VEinteligente/asymentric-lock-box/Asymmetric Lock Box/STEP Files/AcrilicoTapa.STEP

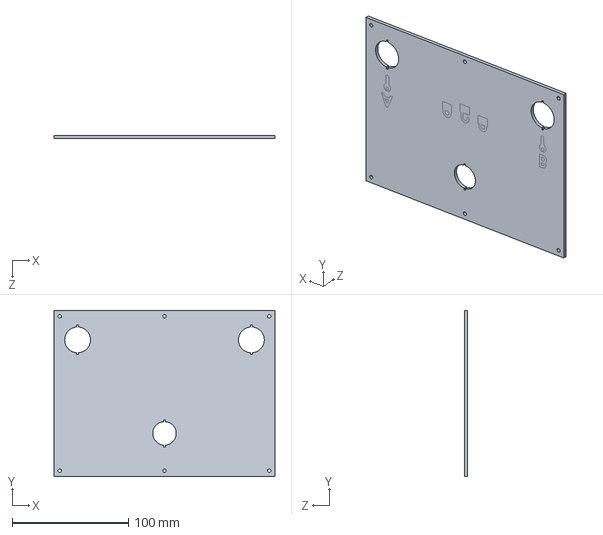
[picture p16: CAD file, 2022-03-03]
Asymmetric Lock Box/STEP Files/AcrilicoTapa.STEP
190.2 x 142.9 x 2.70 mm
