VEinteligente/asymentric-lock-box/Asymmetric Lock Box/STEP Files/BaseCerradura.STEP

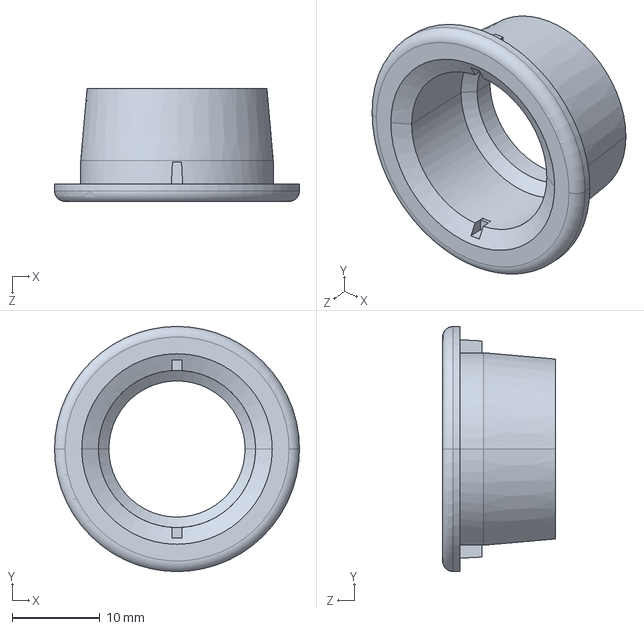
[picture p17: CAD file, 2022-03-03]
Asymmetric Lock Box/STEP Files/BaseCerradura.STEP
28.0 x 28.0 x 12.9 mm
