VEinteligente/asymentric-lock-box/Asymmetric Lock Box/STEP Files/Leva.STEP

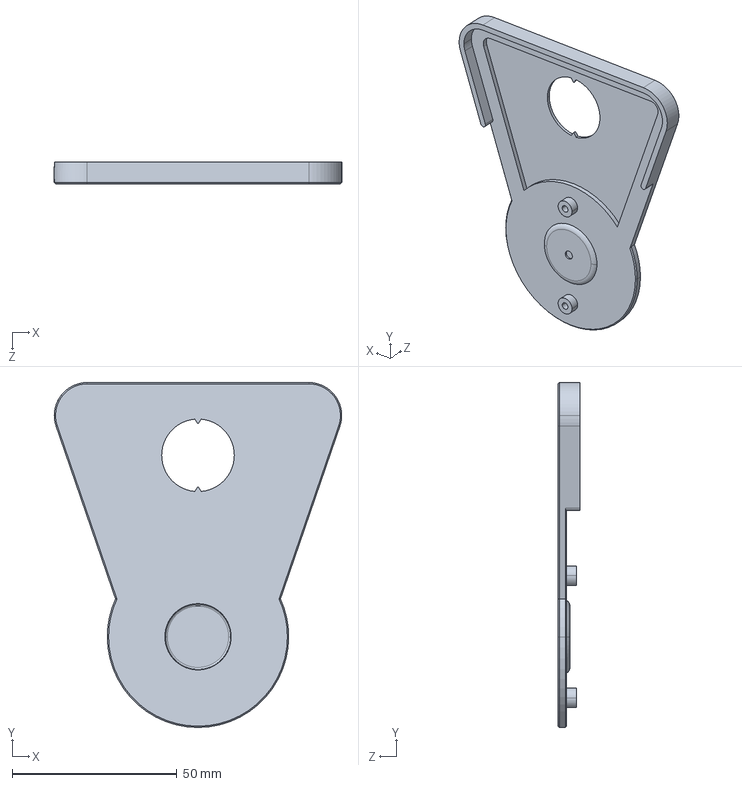
[picture p18: CAD file, 2022-03-03]
Asymmetric Lock Box/STEP Files/Leva.STEP
87.1 x 104.6 x 6.60 mm
