VEinteligente/asymentric-lock-box/Asymmetric Lock Box/STEP Files/BaseLeva.STEP

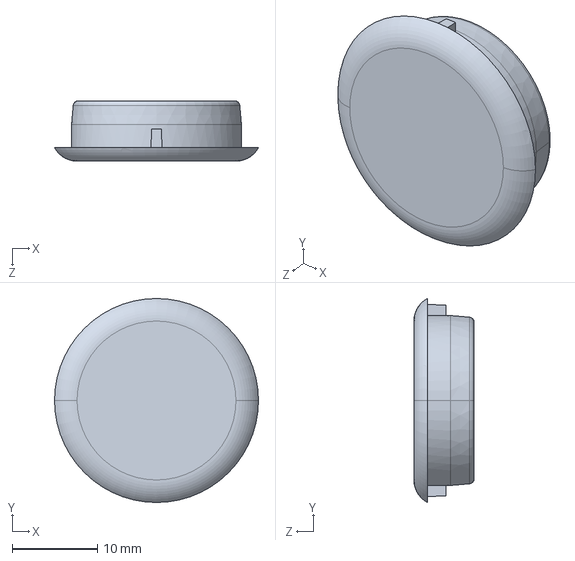
[picture p19: CAD file, 2022-03-03]
Asymmetric Lock Box/STEP Files/BaseLeva.STEP
24.0 x 24.0 x 7.10 mm
