VEinteligente/asymentric-lock-box/Asymmetric Lock Box/STEP Files/LlaveA.STEP

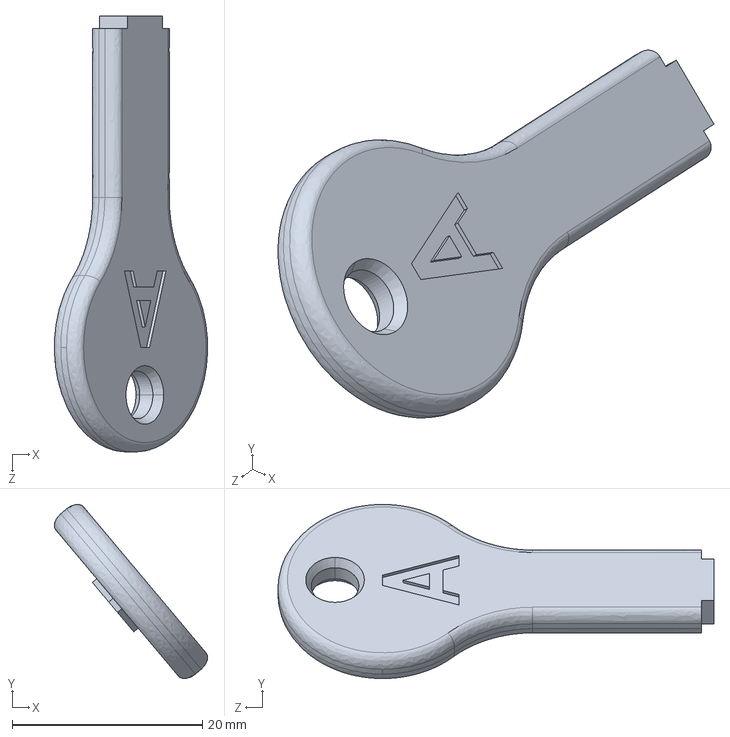
[picture p20: CAD file, 2022-03-03]
Asymmetric Lock Box/STEP Files/LlaveA.STEP
16.1 x 18.3 x 45.8 mm
