VEinteligente/asymentric-lock-box/Asymmetric Lock Box/STEP Files/Nivelador.STEP

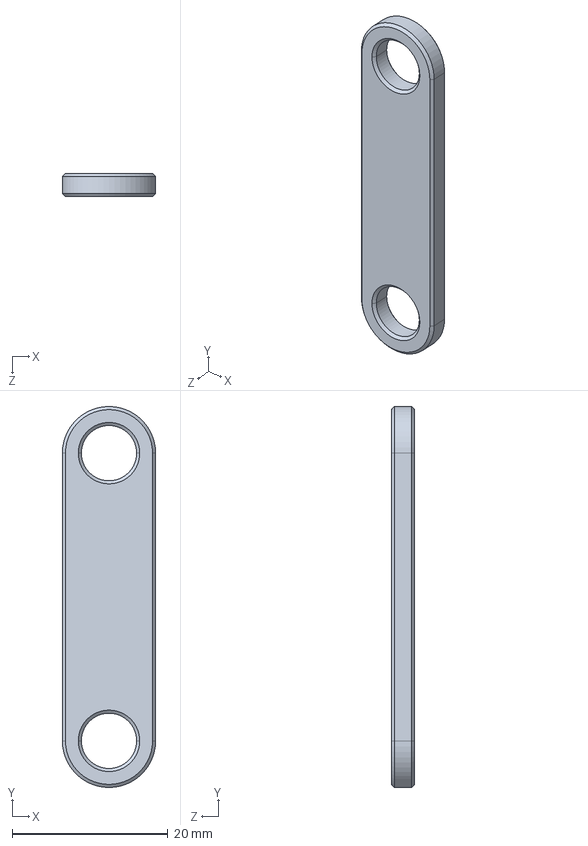
[picture p21: CAD file, 2022-03-03]
Asymmetric Lock Box/STEP Files/Nivelador.STEP
12.0 x 49.0 x 3.00 mm
