VEinteligente/asymentric-lock-box/Asymmetric Lock Box/STEP Files/Marco.STEP

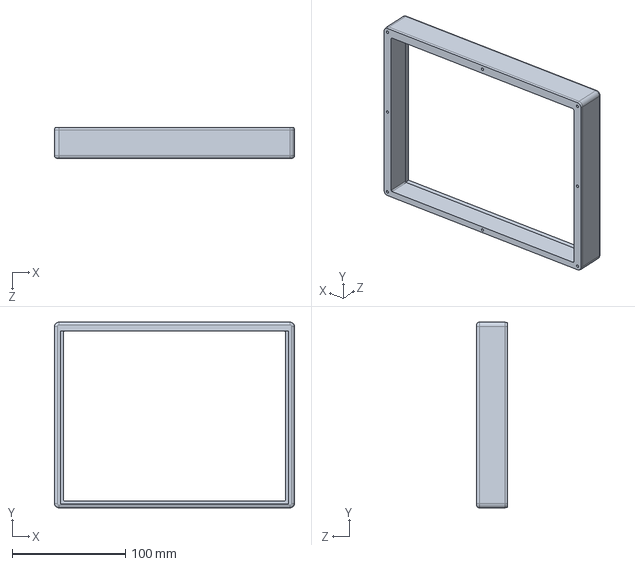
[picture p22: CAD file, 2022-03-03]
Asymmetric Lock Box/STEP Files/Marco.STEP
212.0 x 164.0 x 27.3 mm
